KiranGunathilaka/SynTrack_iot_based_ticketing_machine/Enclosure/Enclosure1/TFT LCD 2.4 inch ILI9341.step

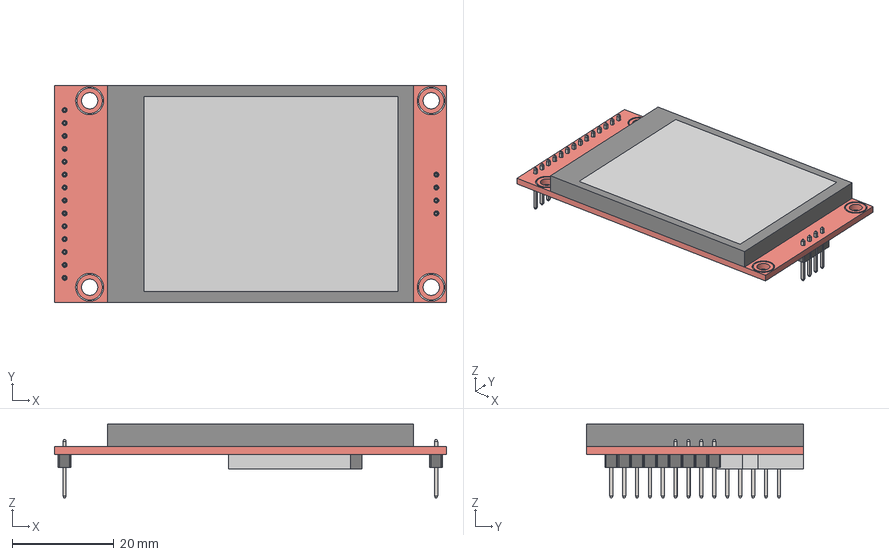
[picture p77: CAD file, 2025-08-10]
Enclosure/Enclosure1/TFT LCD 2.4 inch ILI9341.step
77.2 x 42.7 x 14.5 mm
1x1_Pin_Header_2.54mm x 4
1x1_Pin_Header_2.54mm_1 x 14
