KiranGunathilaka/SynTrack_iot_based_ticketing_machine/Enclosure/Enclosure1/CH340E.stp

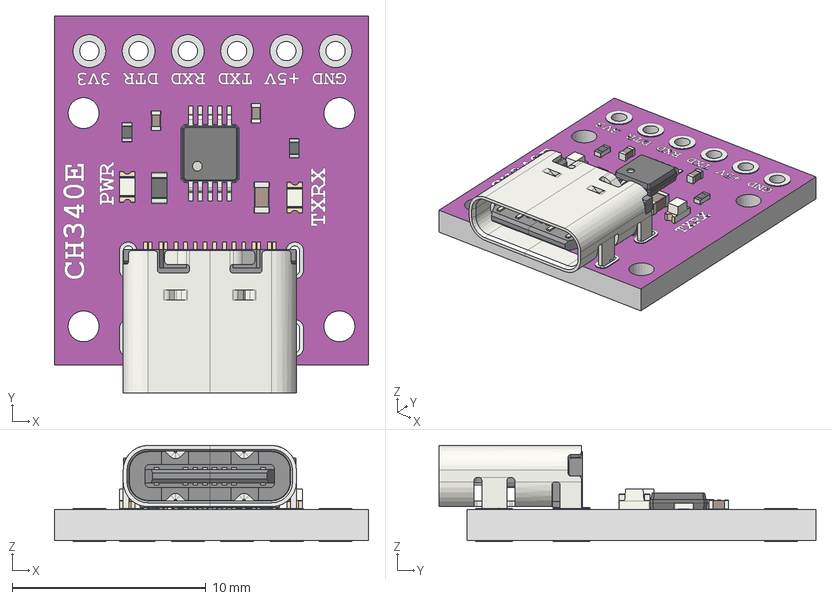
[picture p78: CAD file, 2025-08-10]
Enclosure/Enclosure1/CH340E.stp
16.2 x 19.4 x 4.96 mm
CH340E_1
C_0402_1005Metric x 2
C_0603_1608Metric
Fuse_0603_1608Metric
LED_0603_1608Metric_Castellated x 2
MSOP_10_3x3mm_P05mm
R_0402_1005Metric x 2
USB_C_Receptacle_16P_TopMnt_Horizontal_GCT_USB4105-xx-A
