KiranGunathilaka/SynTrack_iot_based_ticketing_machine/Enclosure/Enclosure1/sf_thermal_printer.SLDPRT

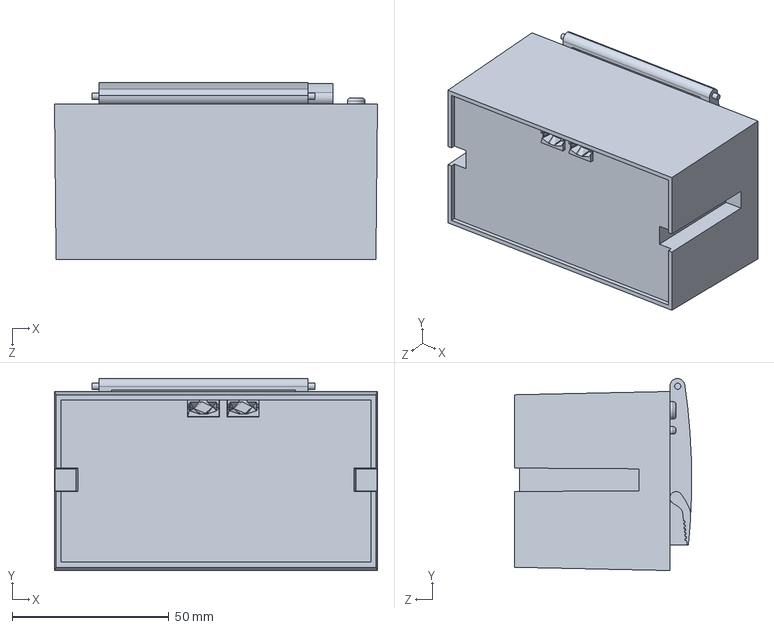
[picture p79: CAD file, 2025-08-10]
Enclosure/Enclosure1/sf_thermal_printer.SLDPRT
103.0 x 61.3 x 56.5 mm
