KiranGunathilaka/SynTrack_iot_based_ticketing_machine/Enclosure/Enclosure1/Bottom.SLDPRT

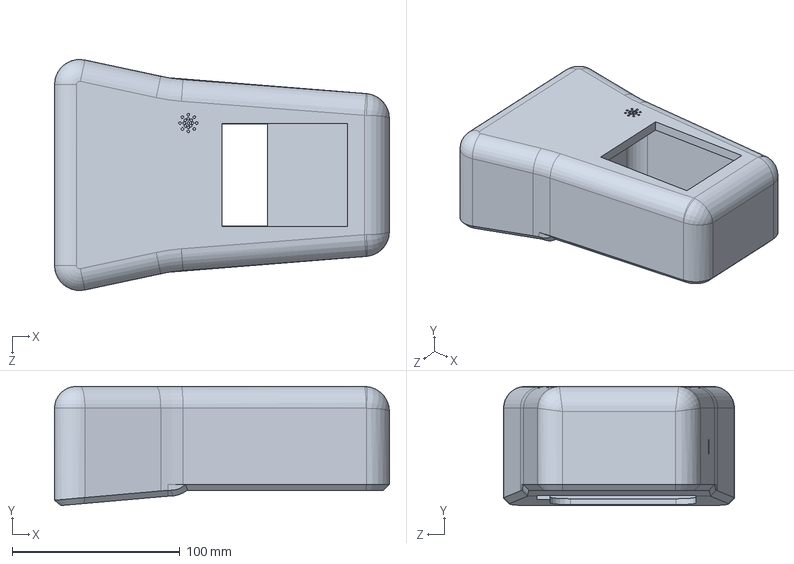
[picture p80: CAD file, 2025-08-10]
Enclosure/Enclosure1/Bottom.SLDPRT
199.9 x 71.1 x 137.9 mm
