KiranGunathilaka/SynTrack_iot_based_ticketing_machine/Enclosure/Enclosure1/Assem1.STL

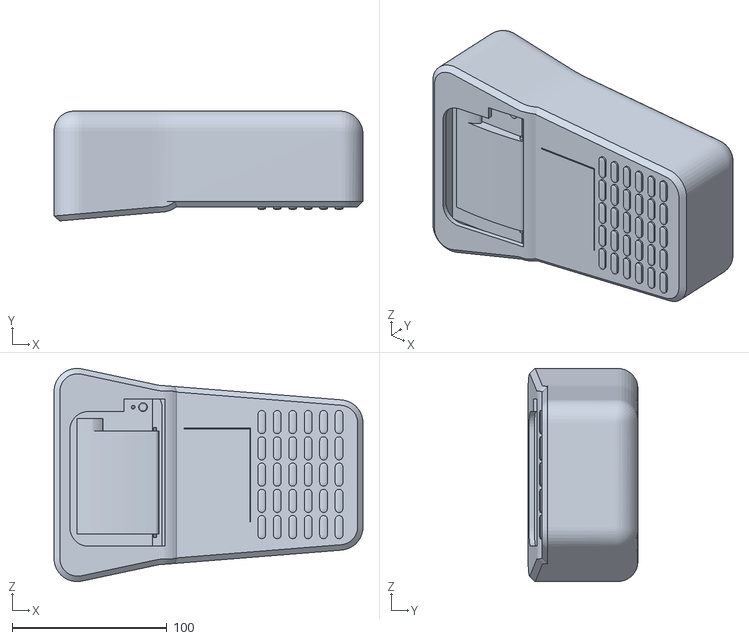
[picture p81: CAD file, 2025-08-10]
Enclosure/Enclosure1/Assem1.STL
199.9 x 71.1 x 137.9
