KiranGunathilaka/SynTrack_iot_based_ticketing_machine/Enclosure/Enclosure1/base.SLDPRT

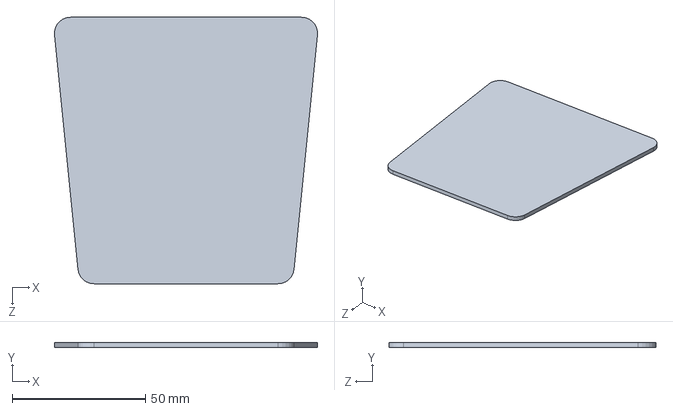
[picture p82: CAD file, 2025-08-10]
Enclosure/Enclosure1/base.SLDPRT
98.7 x 2.00 x 100.0 mm
