KiranGunathilaka/SynTrack_iot_based_ticketing_machine/STM32_CodeBase/Core/Src/LCDController.c

/*
 * LCDController.c
 *
 *  Created on: Sep 28, 2023
 *      Author: controllerstech
 */

/*********************
 *      INCLUDES
 *********************/
#include "LCDController.h"
#include <stdbool.h>
#include "main.h"
#include "ili9341.h"

/*********************
 *      DEFINES
 *********************/
#define MY_DISP_HOR_RES    320
#define MY_DISP_VER_RES    240

/**********************
 *      TYPEDEFS
 **********************/

/**********************
 *  STATIC PROTOTYPES
 **********************/
static void disp_init(void);

static void disp_flush(lv_disp_drv_t *disp_drv, const lv_area_t *area,
		lv_color_t *color_p);
//static void gpu_fill(lv_disp_drv_t * disp_drv, lv_color_t * dest_buf, lv_coord_t dest_width,
//        const lv_area_t * fill_area, lv_color_t color);

/**********************
 *  STATIC VARIABLES
 **********************/

static lv_disp_drv_t disp_drv; /*Descriptor of a display driver*/

//static int32_t x1_flush;
//static int32_t y1_flush;
//static int32_t x2_flush;
//static int32_t y2_fill;
//static int32_t y_fill_act;
//static const lv_color_t * buf_to_flush;

/**********************
 *      MACROS
 **********************/

/**********************
 *   GLOBAL FUNCTIONS
 **********************/

void lv_port_disp_init(void) {
	/*-------------------------
	 * Initialize your display
	 * -----------------------*/
	disp_init();

	/*-----------------------------
	 * Create a buffer for drawing
	 *----------------------------*/

	/**
	 * LVGL requires a buffer where it internally draws the widgets.
	 * Later this buffer will passed to your display driver's `flush_cb` to copy its content to your display.
	 * The buffer has to be greater than 1 display row
	 *
	 * There are 3 buffering configurations:
	 * 1. Create ONE buffer:
	 *      LVGL will draw the display's content here and writes it to your display
	 *
	 * 2. Create TWO buffer:
	 *      LVGL will draw the display's content to a buffer and writes it your display.
	 *      You should use DMA to write the buffer's content to the display.
	 *      It will enable LVGL to draw the next part of the screen to the other buffer while
	 *      the data is being sent form the first buffer. It makes rendering and flushing parallel.
	 *
	 * 3. Double buffering
	 *      Set 2 screens sized buffers and set disp_drv.full_refresh = 1.
	 *      This way LVGL will always provide the whole rendered screen in `flush_cb`
	 *      and you only need to change the frame buffer's address.
	 */

	/* Example for 1) */
	static lv_disp_draw_buf_t draw_buf_dsc_1;
	static lv_color_t buf_1[MY_DISP_HOR_RES * 10]; /*A buffer for 10 rows*/
	lv_disp_draw_buf_init(&draw_buf_dsc_1, buf_1, NULL, MY_DISP_HOR_RES * 10); /*Initialize the display buffer*/

	/* Example for 2) */
//    static lv_disp_draw_buf_t draw_buf_dsc_2;
//    static lv_color_t buf_2_1[MY_DISP_HOR_RES * 80];                        /*A buffer for 80 rows*/
//    static lv_color_t buf_2_2[MY_DISP_HOR_RES * 80];                        /*An other buffer for 80 rows*/
//    lv_disp_draw_buf_init(&draw_buf_dsc_2, buf_2_1, buf_2_2, MY_DISP_HOR_RES * 80);   /*Initialize the display buffer*/

	/*-----------------------------------
	 * Register the display in LVGL
	 *----------------------------------*/

	lv_disp_drv_init(&disp_drv); /*Basic initialization*/

	/*Set up the functions to access to your display*/

	/*Set the resolution of the display*/
	disp_drv.hor_res = MY_DISP_HOR_RES;
	disp_drv.ver_res = MY_DISP_VER_RES;

	/*Used to copy the buffer's content to the display*/
	disp_drv.flush_cb = disp_flush;

	/*Set a display buffer*/
	disp_drv.draw_buf = &draw_buf_dsc_1;

	/*Required for Example 3)*/
	//disp_drv.full_refresh = 1;
	/* Fill a memory array with a color if you have GPU.
	 * Note that, in lv_conf.h you can enable GPUs that has built-in support in LVGL.
	 * But if you have a different GPU you can use with this callback.*/
	//disp_drv.gpu_fill_cb = gpu_fill;
	/*Finally register the driver*/
	lv_disp_drv_register(&disp_drv);
}

/**********************
 *   STATIC FUNCTIONS
 **********************/

/*Initialize your display and the required peripherals.*/
static void disp_init(void) {
	ILI9341_Init();
}

volatile bool disp_flush_enabled = true;

/* Enable updating the screen (the flushing process) when disp_flush() is called by LVGL
 */
void disp_enable_update(void) {
	disp_flush_enabled = true;
}

/* Disable updating the screen (the flushing process) when disp_flush() is called by LVGL
 */
void disp_disable_update(void) {
	disp_flush_enabled = false;
}

/*Flush the content of the internal buffer the specific area on the display
 *You can use DMA or any hardware acceleration to do this operation in the background but
 *'lv_disp_flush_ready()' has to be called when finished.*/
static void disp_flush(lv_disp_drv_t *disp_drv, const lv_area_t *area,
		lv_color_t *color_p) {
	//Set the drawing region
	ILI9341_SetWindow(area->x1, area->y1, area->x2, area->y2);

	int height = area->y2 - area->y1 + 1;
	int width = area->x2 - area->x1 + 1;

	ILI9341_DrawBitmap(width, height, (uint8_t*) color_p);
	//ILI9341_DrawBitmapDMA(width, height, (uint8_t *)color_p);
	/*IMPORTANT!!!
	 *Inform the graphics library that you are ready with the flushing*/
	lv_disp_flush_ready(disp_drv);
}

void HAL_SPI_TxCpltCallback(SPI_HandleTypeDef *hspi) {
	lv_disp_flush_ready(&disp_drv);
//	ILI9341_EndOfDrawBitmap();
}
